JustgeekDE/gatorV2/hw/singleGates/1-BitSelect.brd

## EAGLE design hw/singleGates/1-BitSelect.brd (2016-04-05)

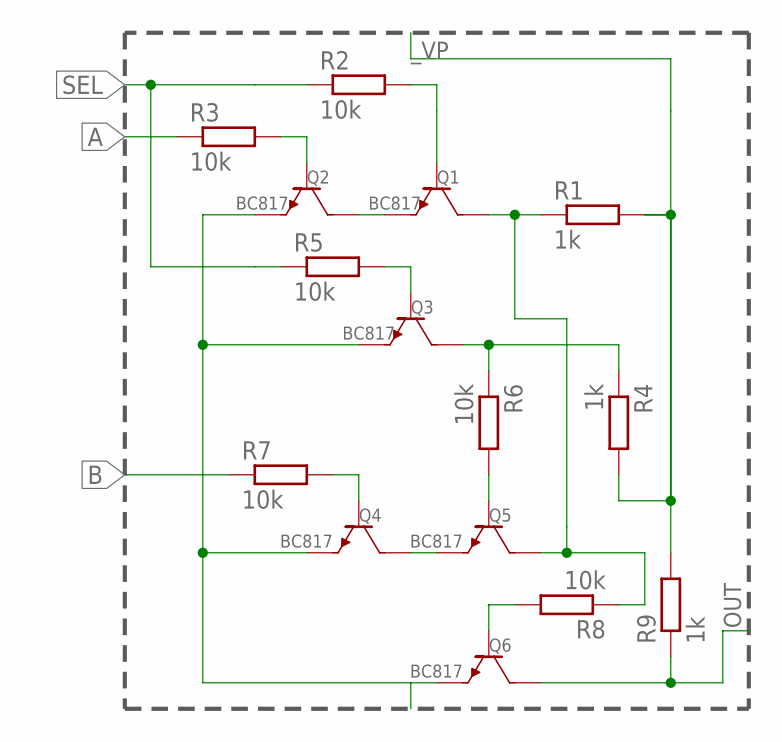
[picture p14: schematic 1-BitSelect.sch]

Parts:
Q1, Q2, Q3, Q4, Q5, Q6: BC817; SOT23
R1, R4, R9: 1k; R0603
R2, R3, R5, R6, R7, R8: 10k; R0603

Connections:
A: R3.1
B: R7.1
I-S2: Q3.P$3 (COLLECTOR), R4.1, R6.1
unnamed: Q1.P$1 (BASE), R2.2
unnamed: Q2.P$1 (BASE), R3.2
unnamed: Q1.P$2 (EMITTER), Q2.P$3 (COLLECTOR)
unnamed: Q5.P$1 (BASE), R6.2
unnamed: Q4.P$1 (BASE), R7.2
unnamed: Q4.P$3 (COLLECTOR), Q5.P$2 (EMITTER)
unnamed: Q6.P$1 (BASE), R8.2
unnamed: Q3.P$1 (BASE), R5.2
OUT: Q6.P$3 (COLLECTOR), R9.1
SEL: R2.1, R5.1
SEL_INT1: Q1.P$3 (COLLECTOR), Q5.P$3 (COLLECTOR), R1.1, R8.1
_VN: Q2.P$2 (EMITTER), Q3.P$2 (EMITTER), Q4.P$2 (EMITTER), Q6.P$2 (EMITTER)
_VP: R1.2, R4.2, R9.2

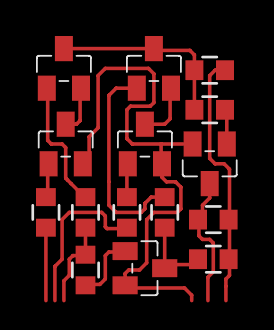
[picture p15: board 1-BitSelect.brd from above]

Board: 2 copper layers, 15 parts (0 on the bottom side), 14 nets.
