JustgeekDE/gatorV2/hw/singleGates/single-gates-SMD.brd

## EAGLE design hw/singleGates/single-gates-SMD.brd (2016-03-27)

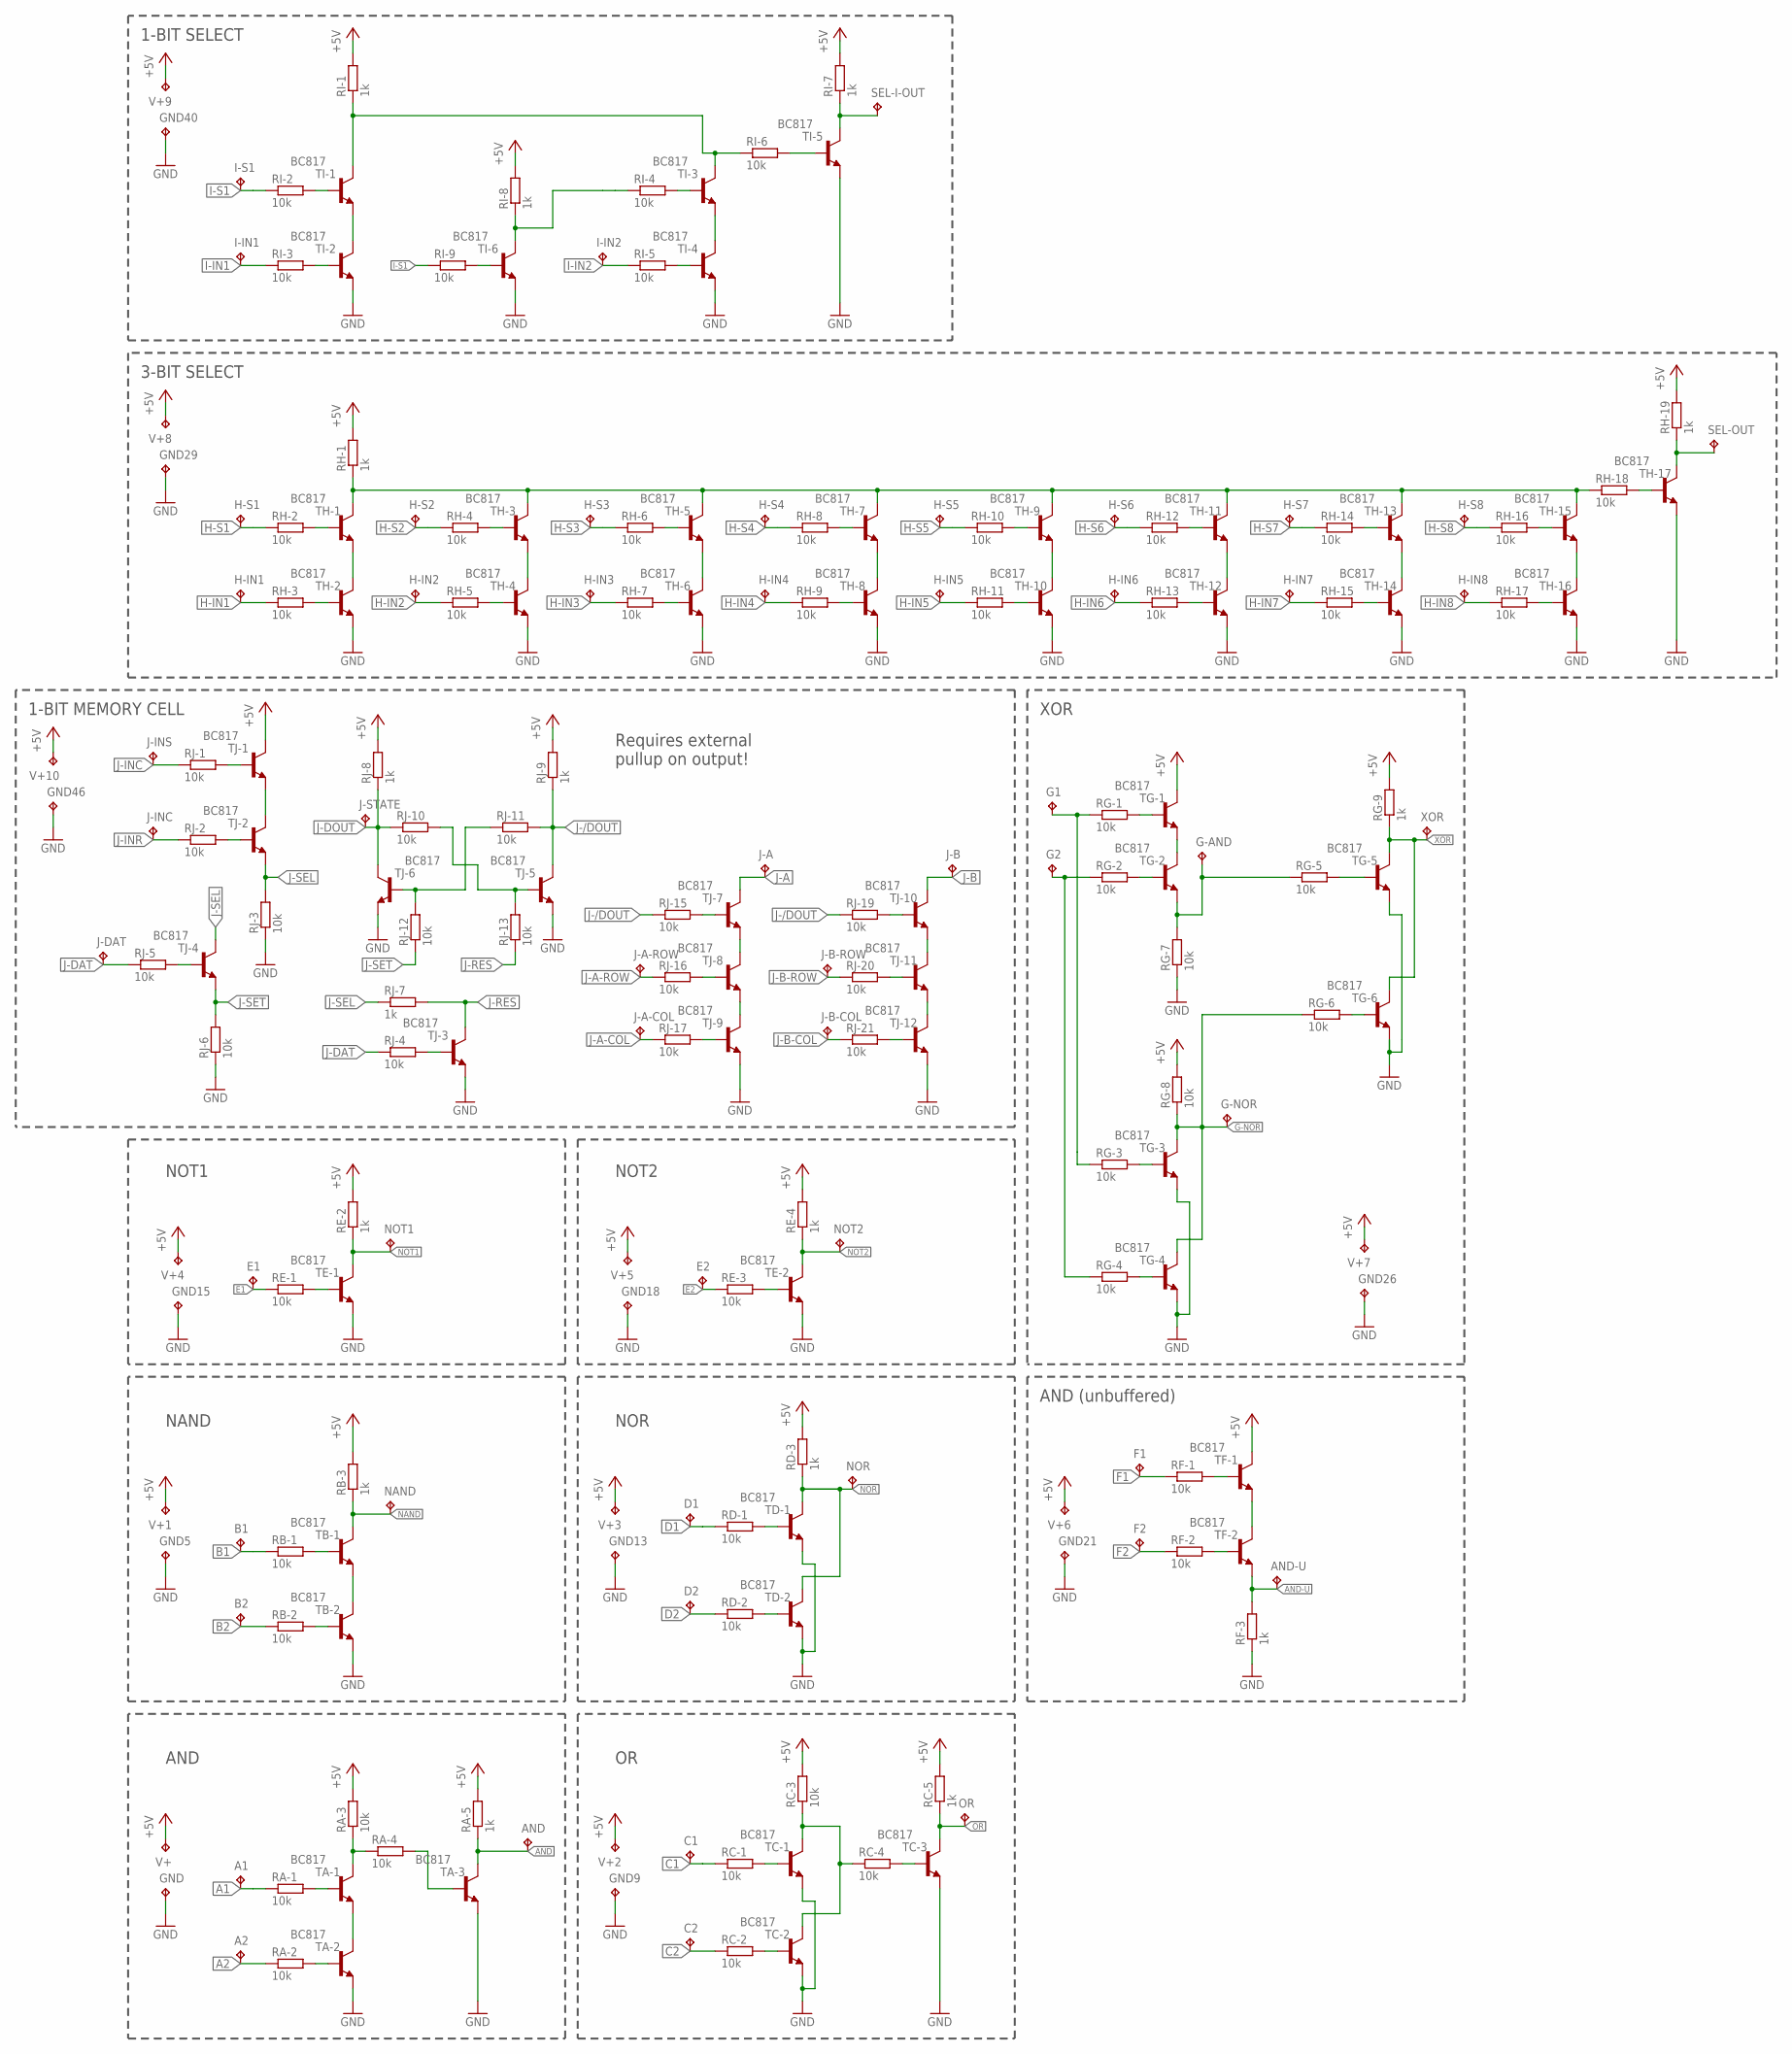
[picture p16: schematic single-gates-SMD.sch]

Parts:
A1, A2: TPTP07R; TP07R
AND: TPTP07R; TP07R
AND-U: TPTP07R; TP07R
B1, B2: TPTP07R; TP07R
C1, C2: TPTP07R; TP07R
D1, D2: TPTP07R; TP07R
E1, E2: TPTP07R; TP07R
F1, F2: TPTP07R; TP07R
G1, G2: TPTP07R; TP07R
G-AND: TPTP07R; TP07R
G-NOR: TPTP07R; TP07R
GND, GND5, GND9, GND13, GND15, GND18, GND21, GND26, GND29, GND40, GND46: TPTP07R; TP07R
H-IN1, H-IN2, H-IN3, H-IN4, H-IN5, H-IN6, H-IN7, H-IN8: TPTP07R; TP07R
H-S1, H-S2, H-S3, H-S4, H-S5, H-S6, H-S7, H-S8: TPTP07R; TP07R
I-IN1, I-IN2: TPTP07R; TP07R
I-S1: TPTP07R; TP07R
J-A: TPTP07R; TP07R
J-A-COL: TPTP07R; TP07R
J-A-ROW: TPTP07R; TP07R
J-B: TPTP07R; TP07R
J-B-COL: TPTP07R; TP07R
J-B-ROW: TPTP07R; TP07R
J-DAT: TPTP07R; TP07R
J-INC: TPTP07R; TP07R
J-INS: TPTP07R; TP07R
J-STATE: TPTP07R; TP07R
NAND: TPTP07R; TP07R
NOR: TPTP07R; TP07R
NOT1, NOT2: TPTP07R; TP07R
OR: TPTP07R; TP07R
RA-1, RA-2, RA-3, RA-4: 10k; R0603
RA-5: 1k; R0603
RB-1, RB-2: 10k; R0603
RB-3: 1k; R0603
RC-1, RC-2, RC-3, RC-4: 10k; R0603
RC-5: 1k; R0603
RD-1, RD-2: 10k; R0603
RD-3: 1k; R0603
RE-1, RE-3: 10k; R0603
RE-2, RE-4: 1k; R0603
RF-1, RF-2: 10k; R0603
RF-3: 1k; R0603
RG-1, RG-2, RG-3, RG-4, RG-5, RG-6, RG-7, RG-8: 10k; R0603
RG-9: 1k; R0603
RH-1, RH-19: 1k; R0603
RH-2, RH-3, RH-4, RH-5, RH-6, RH-7, RH-8, RH-9, RH-10, RH-11, RH-12, RH-13, RH-14, RH-15, RH-16, RH-17, RH-18: 10k; R0603
RI-1, RI-7, RI-8: 1k; R0603
RI-2, RI-3, RI-4, RI-5, RI-6, RI-9: 10k; R0603
RJ-1, RJ-2, RJ-3, RJ-4, RJ-5, RJ-6, RJ-10, RJ-11, RJ-12, RJ-13, RJ-15, RJ-16, RJ-17, RJ-19, RJ-20, RJ-21: 10k; R0603
RJ-7, RJ-8, RJ-9: 1k; R0603
SEL-I-OUT: TPTP07R; TP07R
SEL-OUT: TPTP07R; TP07R
TA-1, TA-2, TA-3: BC817; SOT23-BEC
TB-1, TB-2: BC817; SOT23-BEC
TC-1, TC-2, TC-3: BC817; SOT23-BEC
TD-1, TD-2: BC817; SOT23-BEC
TE-1, TE-2: BC817; SOT23-BEC
TF-1, TF-2: BC817; SOT23-BEC
TG-1, TG-2, TG-3, TG-4, TG-5, TG-6: BC817; SOT23-BEC
TH-1, TH-2, TH-3, TH-4, TH-5, TH-6, TH-7, TH-8, TH-9, TH-10, TH-11, TH-12, TH-13, TH-14, TH-15, TH-16, TH-17: BC817; SOT23-BEC
TI-1, TI-2, TI-3, TI-4, TI-5, TI-6: BC817; SOT23-BEC
TJ-1, TJ-2, TJ-3, TJ-4, TJ-5, TJ-6, TJ-7, TJ-8, TJ-9, TJ-10, TJ-11, TJ-12: BC817; SOT23-BEC
V+, V+1, V+2, V+3, V+4, V+5, V+6, V+7, V+8, V+9, V+10: TPTP07R; TP07R
XOR: TPTP07R; TP07R

Connections:
+5V: RA-3.2, RA-5.2, RB-3.2, RC-3.2, RC-5.2, RD-3.2, RE-2.2, RE-4.2, RG-8.2, RG-9.2, RH-1.2, RH-19.2, RI-1.2, RI-7.2, RI-8.2, RJ-8.2, RJ-9.2, TF-1.C, TG-1.C, TJ-1.C, V+.TP, V+1.TP, V+2.TP, V+3.TP, V+4.TP, V+5.TP, V+6.TP, V+7.TP, V+8.TP, V+9.TP, V+10.TP
A1: A1.TP, RA-1.1
A2: A2.TP, RA-2.1
AND: AND.TP, RA-5.1, TA-3.C
AND-U: AND-U.TP, RF-3.2, TF-2.E
B1: B1.TP, RB-1.1
B2: B2.TP, RB-2.1
C1: C1.TP, RC-1.1
C2: C2.TP, RC-2.1
D1: D1.TP, RD-1.1
D2: D2.TP, RD-2.1
E1: E1.TP, RE-1.1
E2: E2.TP, RE-3.1
F1: F1.TP, RF-1.1
F2: F2.TP, RF-2.1
G-AND: G-AND.TP, RG-5.1, RG-7.2, TG-2.E
G-NOR: G-NOR.TP, RG-6.1, RG-8.1, TG-3.C, TG-4.C
GND: GND.TP, GND5.TP, GND9.TP, GND13.TP, GND15.TP, GND18.TP, GND21.TP, GND26.TP, GND29.TP, GND40.TP, GND46.TP, RF-3.1, RG-7.1, RJ-3.1, RJ-6.1, TA-2.E, TA-3.E, TB-2.E, TC-1.E, TC-2.E, TC-3.E, TD-1.E, TD-2.E, TE-1.E, TE-2.E, TG-3.E, TG-4.E, TG-5.E, TG-6.E, TH-2.E, TH-4.E, TH-6.E, TH-8.E, TH-10.E, TH-12.E, TH-14.E, TH-16.E, TH-17.E, TI-2.E, TI-4.E, TI-5.E, TI-6.E, TJ-3.E, TJ-5.E, TJ-6.E, TJ-9.E, TJ-12.E
H-IN1: H-IN1.TP, RH-3.1
H-IN2: H-IN2.TP, RH-5.1
H-IN3: H-IN3.TP, RH-7.1
H-IN4: H-IN4.TP, RH-9.1
H-IN5: H-IN5.TP, RH-11.1
H-IN6: H-IN6.TP, RH-13.1
H-IN7: H-IN7.TP, RH-15.1
H-IN8: H-IN8.TP, RH-17.1
H-S1: H-S1.TP, RH-2.1
H-S2: H-S2.TP, RH-4.1
H-S3: H-S3.TP, RH-6.1
H-S4: H-S4.TP, RH-8.1
H-S5: H-S5.TP, RH-10.1
H-S6: H-S6.TP, RH-12.1
H-S7: H-S7.TP, RH-14.1
H-S8: H-S8.TP, RH-16.1
I-IN1: I-IN1.TP, RI-3.1
I-IN2: I-IN2.TP, RI-5.1
I-S1: I-S1.TP, RI-2.1, RI-9.1
I-S2: RI-4.1, RI-8.1, TI-6.C
J-/DOUT: RJ-9.1, RJ-11.2, RJ-15.1, RJ-19.1, TJ-5.C
J-A: J-A.TP, TJ-7.C
J-A-COL: J-A-COL.TP, RJ-17.1
J-A-ROW: J-A-ROW.TP, RJ-16.1
J-B: J-B.TP, TJ-10.C
J-B-COL: J-B-COL.TP, RJ-21.1
J-B-ROW: J-B-ROW.TP, RJ-20.1
J-DAT: J-DAT.TP, RJ-4.1, RJ-5.1
J-DOUT: J-STATE.TP, RJ-8.1, RJ-10.1, TJ-6.C
J-INC: J-INS.TP, RJ-1.1
J-INR: J-INC.TP, RJ-2.1
J-RES: RJ-7.2, RJ-13.1, TJ-3.C
J-SEL: RJ-3.2, RJ-7.1, TJ-2.E, TJ-4.C
J-SET: RJ-6.2, RJ-12.1, TJ-4.E
unnamed: RA-1.2, TA-1.B
unnamed: RA-3.1, RA-4.1, TA-1.C
unnamed: RA-2.2, TA-2.B
unnamed: TA-1.E, TA-2.C
unnamed: RB-1.2, TB-1.B
unnamed: RB-2.2, TB-2.B
unnamed: RC-1.2, TC-1.B
unnamed: TB-1.E, TB-2.C
unnamed: RC-2.2, TC-2.B
unnamed: RC-4.2, TC-3.B
unnamed: RC-3.1, RC-4.1, TC-1.C, TC-2.C
unnamed: RD-1.2, TD-1.B
unnamed: RD-2.2, TD-2.B
unnamed: RE-1.2, TE-1.B
unnamed: RA-4.2, TA-3.B
unnamed: RE-3.2, TE-2.B
unnamed: RF-1.2, TF-1.B
unnamed: RF-2.2, TF-2.B
unnamed: TG-1.E, TG-2.C
unnamed: TF-1.E, TF-2.C
unnamed: RG-1.2, TG-1.B
unnamed: RG-2.2, TG-2.B
unnamed: RG-4.2, TG-4.B
unnamed: RG-3.2, TG-3.B
unnamed: RG-6.2, TG-6.B
unnamed: RG-5.2, TG-5.B
unnamed: RH-2.2, TH-1.B
unnamed: RH-3.2, TH-2.B
unnamed: TH-1.E, TH-2.C
unnamed: G1.TP, RG-1.1, RG-3.1
unnamed: G2.TP, RG-2.1, RG-4.1
unnamed: RH-4.2, TH-3.B
unnamed: RH-5.2, TH-4.B
unnamed: TH-3.E, TH-4.C
unnamed: RH-6.2, TH-5.B
unnamed: RH-7.2, TH-6.B
unnamed: TH-5.E, TH-6.C
unnamed: RH-8.2, TH-7.B
unnamed: RH-9.2, TH-8.B
unnamed: TH-7.E, TH-8.C
unnamed: RH-10.2, TH-9.B
unnamed: RH-11.2, TH-10.B
unnamed: TH-9.E, TH-10.C
unnamed: RH-12.2, TH-11.B
unnamed: RH-13.2, TH-12.B
unnamed: TH-11.E, TH-12.C
unnamed: RH-14.2, TH-13.B
unnamed: RH-15.2, TH-14.B
unnamed: TH-13.E, TH-14.C
unnamed: RH-16.2, TH-15.B
unnamed: RH-17.2, TH-16.B
unnamed: TH-15.E, TH-16.C
unnamed: RI-2.2, TI-1.B
unnamed: RH-18.2, TH-17.B
unnamed: RI-3.2, TI-2.B
unnamed: TI-1.E, TI-2.C
unnamed: RI-4.2, TI-3.B
unnamed: RI-5.2, TI-4.B
unnamed: TI-3.E, TI-4.C
unnamed: RI-6.2, TI-5.B
unnamed: RJ-1.2, TJ-1.B
unnamed: RI-9.2, TI-6.B
unnamed: RJ-2.2, TJ-2.B
unnamed: TJ-1.E, TJ-2.C
unnamed: RJ-4.2, TJ-3.B
unnamed: RJ-5.2, TJ-4.B
unnamed: TJ-10.E, TJ-11.C
unnamed: TJ-7.E, TJ-8.C
unnamed: RJ-11.1, RJ-12.2, TJ-6.B
unnamed: RJ-10.2, RJ-13.2, TJ-5.B
unnamed: TJ-8.E, TJ-9.C
unnamed: RJ-15.2, TJ-7.B
unnamed: RJ-16.2, TJ-8.B
unnamed: RJ-17.2, TJ-9.B
unnamed: TJ-11.E, TJ-12.C
unnamed: RJ-19.2, TJ-10.B
unnamed: RJ-20.2, TJ-11.B
unnamed: RJ-21.2, TJ-12.B
NAND: NAND.TP, RB-3.1, TB-1.C
NOR: NOR.TP, RD-3.1, TD-1.C, TD-2.C
NOT1: NOT1.TP, RE-2.1, TE-1.C
NOT2: NOT2.TP, RE-4.1, TE-2.C
OR: OR.TP, RC-5.1, TC-3.C
SEL_INT: RH-1.1, RH-18.1, TH-1.C, TH-3.C, TH-5.C, TH-7.C, TH-9.C, TH-11.C, TH-13.C, TH-15.C
SEL_INT1: RI-1.1, RI-6.1, TI-1.C, TI-3.C
SEL_OUT: RH-19.1, SEL-OUT.TP, TH-17.C
SEL_OUT1: RI-7.1, SEL-I-OUT.TP, TI-5.C
XOR: RG-9.1, TG-5.C, TG-6.C, XOR.TP

Notes on the sheet:
AND
NAND
NOR
NOT1
NOT2
AND (unbuffered)
XOR
3-BIT SELECT
1-BIT SELECT
1-BIT MEMORY CELL
Requires external pullup on output!

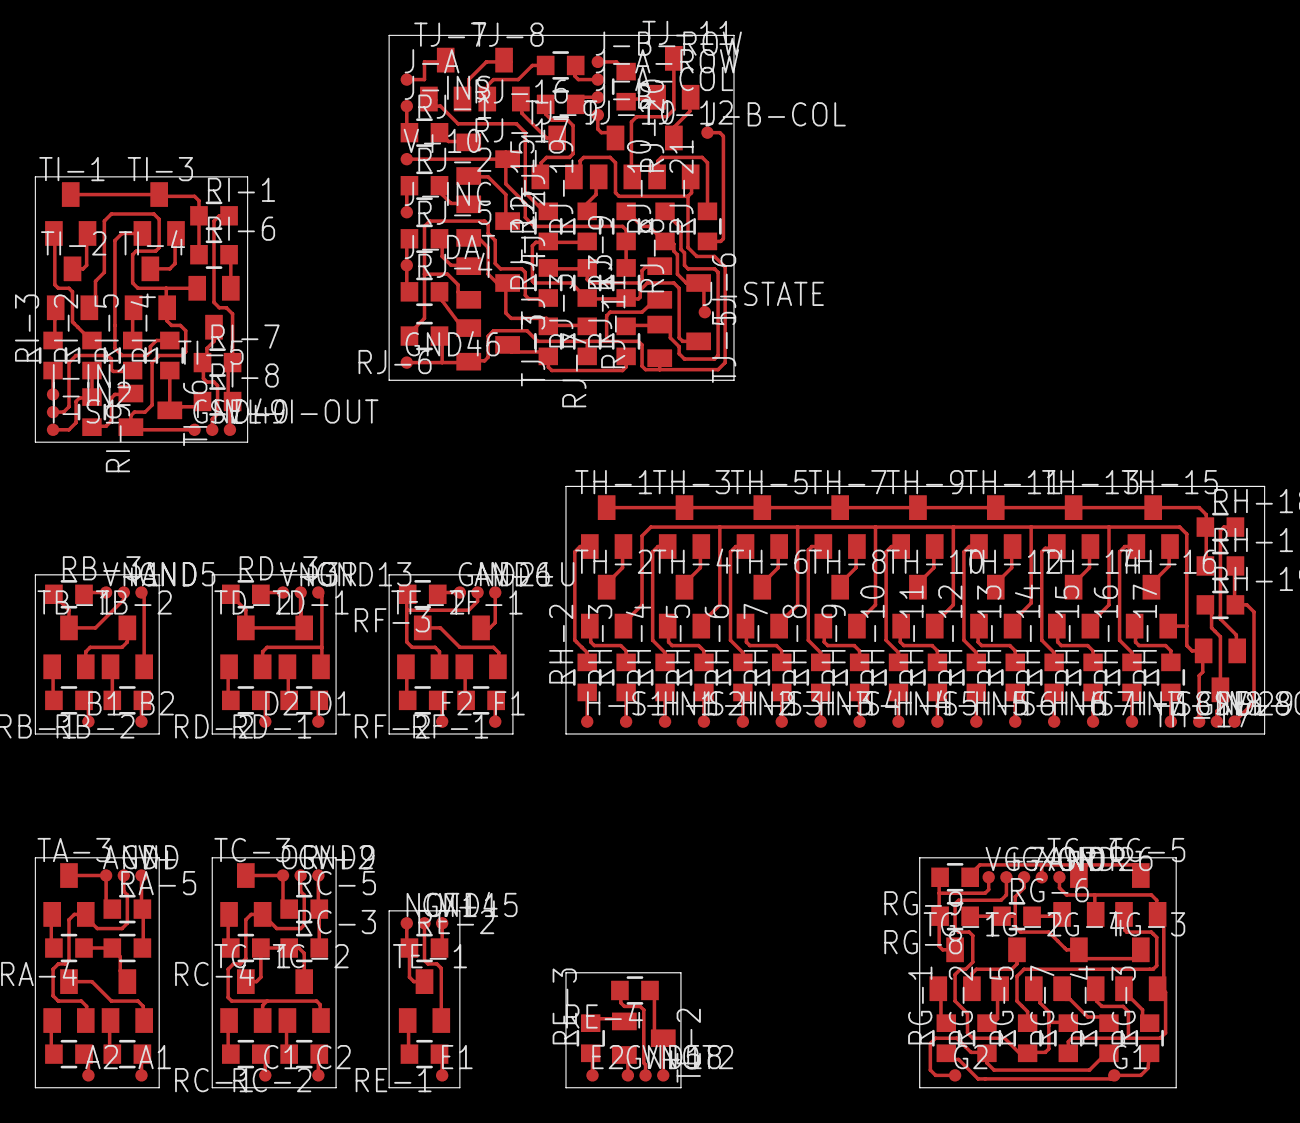
[picture p17: board single-gates-SMD.brd from above]

Board: 2 copper layers, 69.5 x 59.5 mm, 211 parts (0 on the bottom side), 140 nets.
